matthijskooijman/jtagice3-converter-board/JTAGICE3.sch

## KiCad design JTAGICE3.sch (2015-02-12)

Schematic: JTAGICE3.sch

Parts:
ICSP1: AVR-ICSP; Pin_Header_Straight_2x03
JTAG1: AVR-JTAG; Pin_Header_Straight_2x05
JTAG2: AVR-JTAG; Pin_Header_Straight_2x05_Pitch1.27mm_longpads
JTAGICE1: AVR-JTAG; Pin_Header_Straight_2x05_Pitch1.27mm_longpads
SW1: SW_PUSH; SW_PUSH_SMALL
